MakerM0/MagiClick-esp32s3/documents/images/3.gif

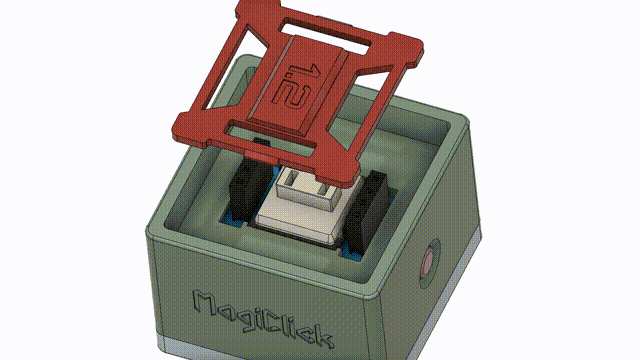
documents/images/3.gif
