MakerM0/MagiClick-esp32s3/documents/images/4.jpg

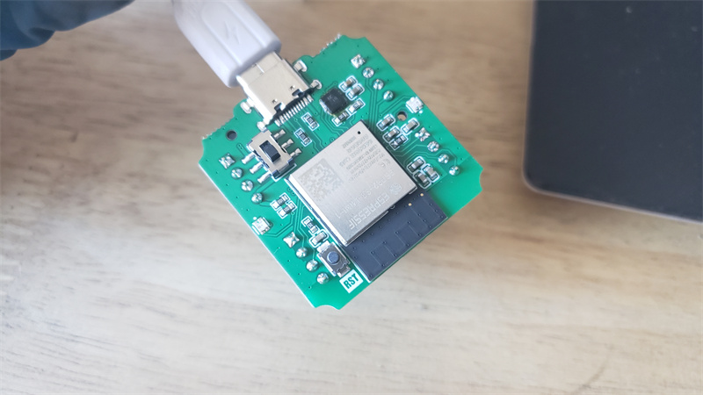
documents/images/4.jpg
