MakerM0/MagiClick-esp32s3/documents/images/5.jpg

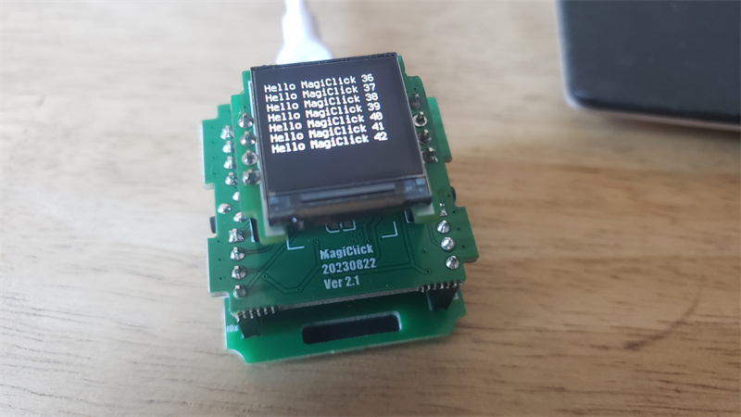
documents/images/5.jpg
