MakerM0/MagiClick-esp32s3/documents/images/18.png

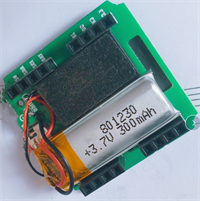
documents/images/18.png
