MakerM0/MagiClick-esp32s3/documents/images/GC9107.png

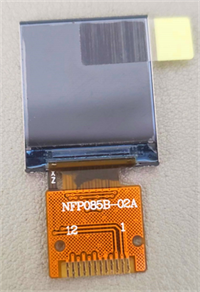
documents/images/GC9107.png
