MakerM0/MagiClick-esp32s3/documents/images/NV3023.png

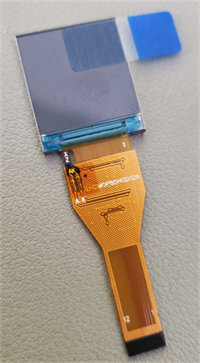
documents/images/NV3023.png
