MakerM0/MagiClick-esp32s3/documents/pin.png

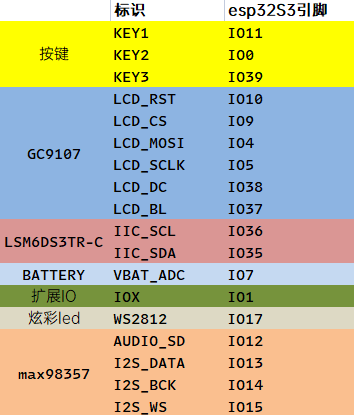
documents/pin.png
