MakerM0/MagiClick-esp32s3/software/circuitpython 8.x/images/bilibili/yijiansanlian.bmp

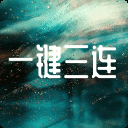
software/circuitpython 8.x/images/bilibili/yijiansanlian.bmp
