MakerM0/MagiClick-esp32s3/software/Arduino/esp32_gfx_dino/dino.wasm.h

unsigned char dino_wasm[] = {
  0x00, 0x61, 0x73, 0x6d, 0x01, 0x00, 0x00, 0x00, 0x01, 0x1b, 0x05, 0x60,
  0x00, 0x01, 0x7d, 0x60, 0x03, 0x7f, 0x7f, 0x7f, 0x00, 0x60, 0x00, 0x00,
  0x60, 0x01, 0x7f, 0x01, 0x7f, 0x60, 0x04, 0x7f, 0x7f, 0x7f, 0x7f, 0x01,
  0x7f, 0x02, 0x1d, 0x02, 0x04, 0x4d, 0x61, 0x74, 0x68, 0x06, 0x72, 0x61,
  0x6e, 0x64, 0x6f, 0x6d, 0x00, 0x00, 0x04, 0x44, 0x69, 0x6e, 0x6f, 0x06,
  0x6d, 0x65, 0x6d, 0x63, 0x70, 0x79, 0x00, 0x01, 0x03, 0x05, 0x04, 0x02,
  0x03, 0x04, 0x02, 0x05, 0x03, 0x01, 0x00, 0x01, 0x06, 0x30, 0x07, 0x7d,
  0x00, 0x43, 0x00, 0x00, 0x00, 0x00, 0x0b, 0x7d, 0x00, 0x43, 0x00, 0x00,
  0x48, 0x42, 0x0b, 0x7f, 0x01, 0x41, 0x00, 0x0b, 0x7f, 0x01, 0x41, 0x00,
  0x0b, 0x7f, 0x01, 0x41, 0x00, 0x0b, 0x7d, 0x01, 0x43, 0x00, 0x00, 0x00,
  0x00, 0x0b, 0x7d, 0x01, 0x43, 0x00, 0x00, 0x00, 0xbf, 0x0b, 0x07, 0x18,
  0x03, 0x03, 0x6d, 0x65, 0x6d, 0x02, 0x00, 0x08, 0x63, 0x6f, 0x6c, 0x6f,
  0x72, 0x35, 0x36, 0x35, 0x00, 0x03, 0x03, 0x72, 0x75, 0x6e, 0x00, 0x05,
  0x08, 0x01, 0x02, 0x0c, 0x01, 0x02, 0x0a, 0x9e, 0x08, 0x04, 0xf5, 0x01,
  0x01, 0x0c, 0x7f, 0x41, 0x07, 0x21, 0x02, 0x41, 0xbb, 0x06, 0x21, 0x07,
  0x03, 0x40, 0x20, 0x01, 0x41, 0x10, 0x49, 0x04, 0x40, 0x20, 0x00, 0x20,
  0x06, 0x2f, 0x01, 0xd0, 0x02, 0x20, 0x01, 0x74, 0x72, 0x21, 0x00, 0x20,
  0x01, 0x41, 0x10, 0x6a, 0x21, 0x01, 0x20, 0x06, 0x41, 0x02, 0x6a, 0x21,
  0x06, 0x0b, 0x20, 0x00, 0x41, 0x01, 0x20, 0x02, 0x74, 0x41, 0x01, 0x6b,
  0x71, 0x21, 0x03, 0x20, 0x00, 0x20, 0x02, 0x76, 0x21, 0x00, 0x20, 0x01,
  0x20, 0x02, 0x6b, 0x21, 0x01, 0x02, 0x40, 0x02, 0x40, 0x02, 0x40, 0x02,
  0x40, 0x02, 0x40, 0x20, 0x09, 0x0e, 0x03, 0x00, 0x01, 0x04, 0x03, 0x0b,
  0x20, 0x03, 0x22, 0x04, 0x45, 0x0d, 0x01, 0x41, 0x01, 0x21, 0x09, 0x41,
  0x04, 0x21, 0x02, 0x0c, 0x04, 0x0b, 0x20, 0x07, 0x20, 0x03, 0x3a, 0x00,
  0x00, 0x20, 0x07, 0x41, 0x01, 0x6a, 0x21, 0x07, 0x20, 0x04, 0x41, 0x01,
  0x6b, 0x22, 0x04, 0x0d, 0x03, 0x0b, 0x41, 0x02, 0x21, 0x09, 0x41, 0x07,
  0x21, 0x02, 0x0c, 0x02, 0x0b, 0x20, 0x07, 0x20, 0x07, 0x20, 0x05, 0x6b,
  0x20, 0x07, 0x20, 0x03, 0x6a, 0x22, 0x07, 0x10, 0x01, 0x41, 0x00, 0x21,
  0x09, 0x0c, 0x01, 0x0b, 0x20, 0x03, 0x21, 0x05, 0x41, 0x03, 0x21, 0x09,
  0x20, 0x06, 0x41, 0xee, 0x03, 0x49, 0x0d, 0x00, 0x0b, 0x03, 0x40, 0x20,
  0x06, 0x2d, 0x00, 0xcd, 0x02, 0x22, 0x0a, 0x04, 0x40, 0x20, 0x07, 0x20,
  0x0b, 0x3a, 0x00, 0x00, 0x20, 0x07, 0x41, 0x01, 0x6a, 0x20, 0x07, 0x20,
  0x07, 0x20, 0x0a, 0x6a, 0x22, 0x07, 0x10, 0x01, 0x0b, 0x20, 0x0b, 0x45,
  0x21, 0x0b, 0x20, 0x06, 0x41, 0x01, 0x6a, 0x22, 0x06, 0x41, 0xc0, 0x0f,
  0x49, 0x0d, 0x00, 0x0b, 0x0b, 0x2d, 0x00, 0x41, 0xff, 0x01, 0x20, 0x00,
  0x6b, 0x21, 0x00, 0x20, 0x00, 0x41, 0x1f, 0x6c, 0x41, 0xff, 0x01, 0x6e,
  0x20, 0x00, 0x41, 0x3f, 0x6c, 0x41, 0xff, 0x01, 0x6e, 0x41, 0x05, 0x74,
  0x20, 0x00, 0x41, 0x1f, 0x6c, 0x41, 0xff, 0x01, 0x6e, 0x41, 0x0b, 0x74,
  0x72, 0x72, 0x0b, 0xc0, 0x01, 0x01, 0x08, 0x7f, 0x20, 0x02, 0x2d, 0x00,
  0xa9, 0x02, 0x22, 0x04, 0x21, 0x09, 0x20, 0x02, 0x2d, 0x00, 0xaa, 0x02,
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
};
unsigned int dino_wasm_len = 2063;
